kgavvala18/powergloveV2_LockheedMartin/reports/Individual reports/Brint Nielson/Individual Weekly Report 8.pdf

### Individual Weekly Report

Name: Brint Nielson
Team: The Gauntlet
Date: 3/29/2025

Current Status
1. What did you personally work on this past week?
Task | Status | Time Spent
Get driver example files and test drivers | In progress | 2 Hour
Adjust STL files for print casing and print casing | In progress | 3.5 hour

Include screenshots/graphics to illustrate what you did this past week:

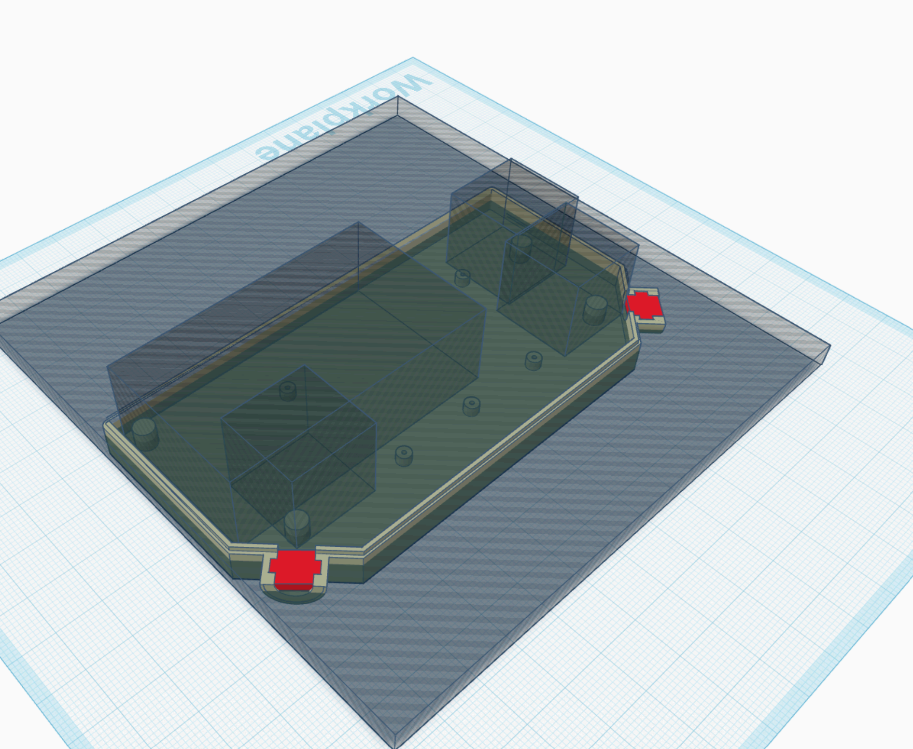
[picture p17: figure]

2. What problems did you run into? What is your plan for them? My 3d printer was giving me some issues but I was able to fix that.
3. What is the current overall project status from your perspective? Putting together for the final prototype/ testing.
4. How is your team functioning from your perspective?

Great we are close to finalizing and being able to test the integrated prototype.

5. What new ideas did you have or skills did you develop this week?
How to properly get my 3d printer to work and now learning how to test drivers.
6. Who was your most awesome team member this week and why?
I would put Will as the awesome team member of the week since he did great job starting the UI.

Plans for Next Week
What are you going to work on this next week?
Driver finalized and working with prototype and print and integrate final 3d prints.
