kgavvala18/powergloveV2_LockheedMartin/reports/Individual reports/Kris_Gavvala/weeklyUpdate3-24.pdf

### Individual Weekly Report

Name: Kris Gavvala
Team: PowerGlove
Date: 3/24/2025

Current Status
1. What did you personally work on this past week?
Task | Status | Time Spent
Implemented mouse clicks over usb hid | finished | 4 hours
Helped set connect all hardware for the prototype | finished | 2 hours

Include screenshots/graphics to illustrate what you did this past week:

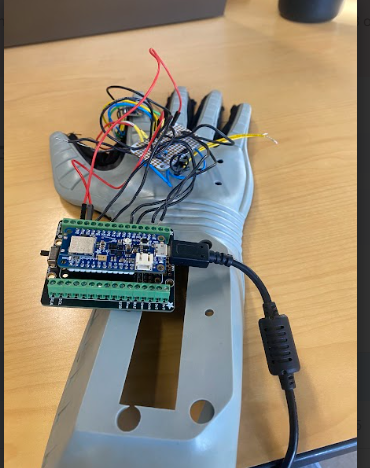
[picture p18: figure]

2. What problems did you run into? What is your plan for them?
Having some problems with keeping the cursor steady due to human movement imprecision. Need to create a dead zone when someone hovers over an object to click it.
3. What is the current overall project status from your perspective?
We are a little behind. We should finish the basic control movements this week and move into gesture control.
4. How is your team functioning from your perspective?
Pretty well. We are splitting up the work well.
5. What new ideas did you have or skills did you develop this week? Explored a little into using usb hid with a wireless transceiver.
6. Who was your most awesome team member this week and why?
Aaron was a great with putting together the prototype. He always shows up outside class to get work done and I really appreciate that.

Plans for Next Week
What are you going to work on this next week?

Going to figure out how to add functionality so that the mouse doesn’t move too much when trying to click.
