kgavvala18/powergloveV2_LockheedMartin/reports/Individual reports/Brint Nielson/Individual Weekly Report 7.pdf

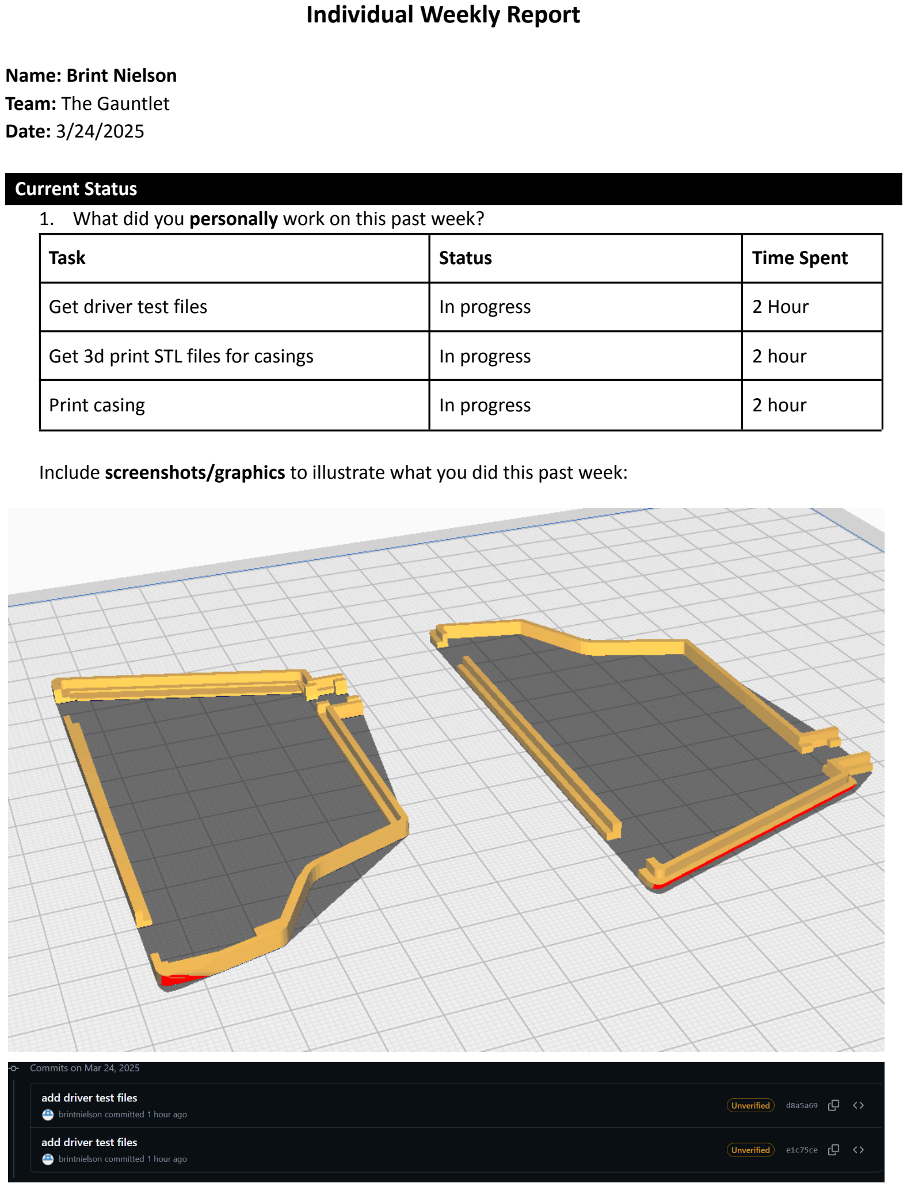
[picture p19: page 1]

### Individual Weekly Report

Name: Brint Nielson
Team: The Gauntlet
Date: 3/24/2025

Current Status
1. What did you personally work on this past week?
Task | Status | Time Spent
Get driver test files | In progress | 2 Hour
Get 3d print STL files for casings | In progress | 2 hour
Print casing | In progress | 2 hour

Include screenshots/graphics to illustrate what you did this past week:

2. What problems did you run into? What is your plan for them?
Was sick the last week but the next week I should be much more free so I will be working on it overtime.
3. What is the current overall project status from your perspective?
The prototype stage and next stage is to make it look good and work even better.
4. How is your team functioning from your perspective?
Great we have been making great progress so far.
5. What new ideas did you have or skills did you develop this week?
I was able to get more 3d print designs and learning more how that works.
6. Who was your most awesome team member this week and why?
I would put Grant for putting together the really small soldering of the encoders.

Plans for Next Week
What are you going to work on this next week?
Finalize driver testing and get a good print going for our casings.
