kgavvala18/powergloveV2_LockheedMartin/reports/Individual reports/Kris_Gavvala/Individual_report_3-17.pdf

### Individual Weekly Report

Name: Kris Gavvala
Team: PowerGlove
Date: 3/17/2025

Current Status
1. What did you personally work on this past week?
Task | Status | Time Spent
Implemented an extended Kalman filter to Process data from IMU | finished | 4 days
Designed the circuit for the laser pointer | finished | 2 hours
Did some planning for gesture features | finished | 2 hours

Include screenshots/graphics to illustrate what you did this past week:

Gyroscope Filtered Data vs measurements:

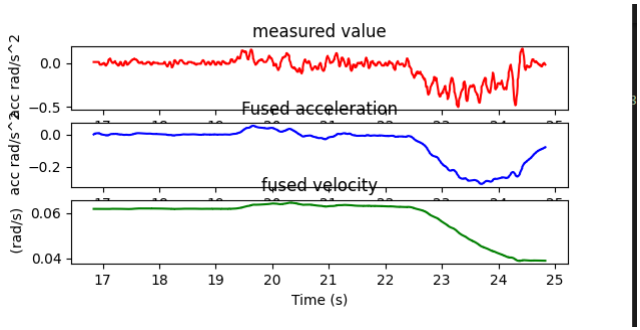
[picture p20: figure]

Arduino C code of Kalman Filter Implementation

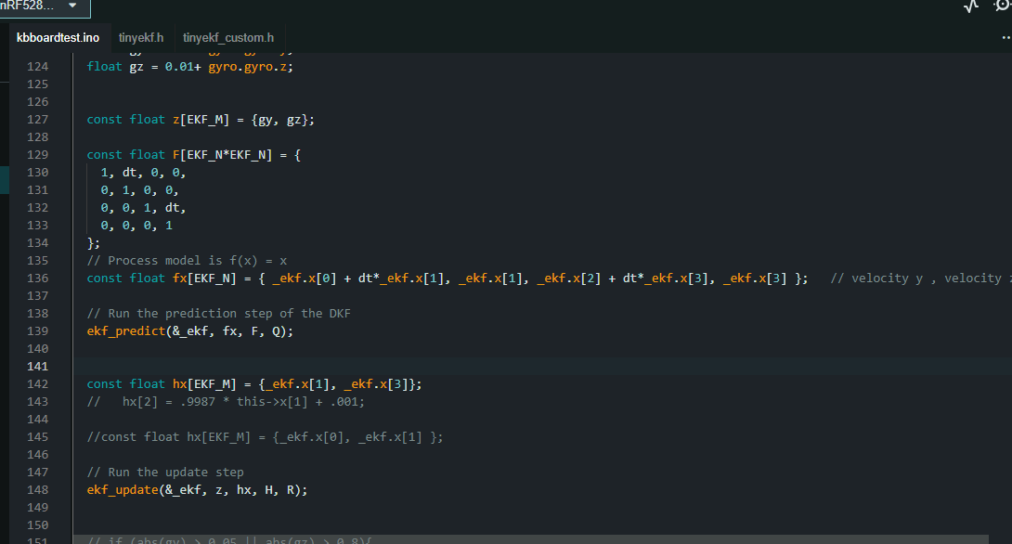
[picture p21: figure]

2. What problems did you run into? What is your plan for them?
We were having trouble with jitter when translating our sensor data into mouse control. To solve this I implemented a kalman filter to smooth the data in real-time for better mouse control.
One problem I still need to solve is getting the glove to keep track of its location in space so it can stay locked onto the mouse without much calibration. I will explore different strategies with the magnetometer to track its initial starting point and motion so that it stays with the mouse.
3. What is the current overall project status from your perspective?
We are slightly behind. We plan to get all current hardware into the glove by the end of this week and start testing the full product.
4. How is your team functioning from your perspective?
We are doing good. We all have defined roles for this week and should be in position to finish up base requirements and move into some stretch goals.
5. What new ideas did you have or skills did you develop this week?
I learned a lot about kalman filters and extended kalman filters. I got some more experience using matlab to test math before putting it into code.

6. Who was your most awesome team member this week and why?
Grant was good this week. He did some good work with coding the buttons.

Plans for Next Week
What are you going to work on this next week?
- Moving parts into the glove
- Tuning the cursor movement so that it accurately stays with the mouse even when the glove’s angular acceleration takes it off-screen.
- Design 3d printed housing to put both accelerometer and laser on the finger.
- Tune mouse movement so that it accounts for both accelerometer movement and gyroscope movement.
