kgavvala18/powergloveV2_LockheedMartin/reports/Individual reports/Brint Nielson/Individual Weekly Report 5.pdf

### Individual Weekly Report

Name: Brint Nielson
Team: The Gauntlet
Date: 3/3/2025

Current Status
1. What did you personally work on this past week?
Task | Status | Time Spent
Get left ctrl modifiers to work to allow more versatility in inputs from the glove | Complete | 1.5 hours
Work on getting integrate mouse movement to be more smooth | In progress | 2 hours
Start driver development | In progress | 50 mins

Include screenshots/graphics to illustrate what you did this past week:

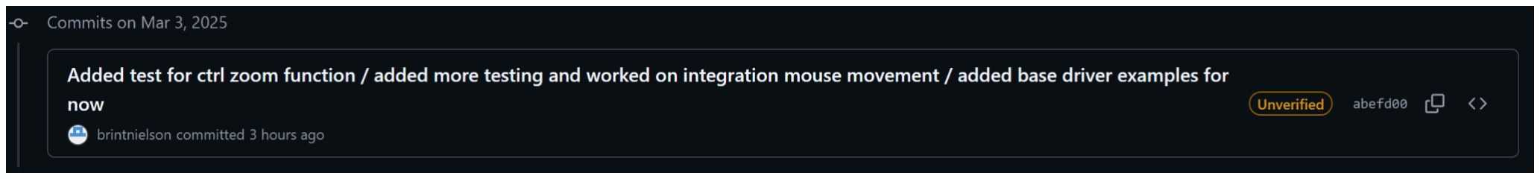
[picture p24: figure]

2. What problems did you run into? What is your plan for them?
So far just slower than expected progress for mouse integration but planning to work on it more this week since I should have more time this week after my test then last week.
3. What is the current overall project status from your perspective?
Finished most testing of hardware and now integrating the hardware and refining the software to make it work better.
4. How is your team functioning from your perspective?
Great we have been making good progress so far.
5. What new ideas did you have or skills did you develop this week?
Learned how drivers work and how to further make our mouse controls work the way we want them too.
6. Who was your most awesome team member this week and why?

I would put Aaron since he sent us a video update for how the glove had the flex sensors in it and worked with it.

Plans for Next Week
What are you going to work on this next week?
I want to get mouse movement working much better and finish learning about drivers and hopefully finish those up.
