kgavvala18/powergloveV2_LockheedMartin/reports/Individual reports/Aaron/IndividualReport8.pdf

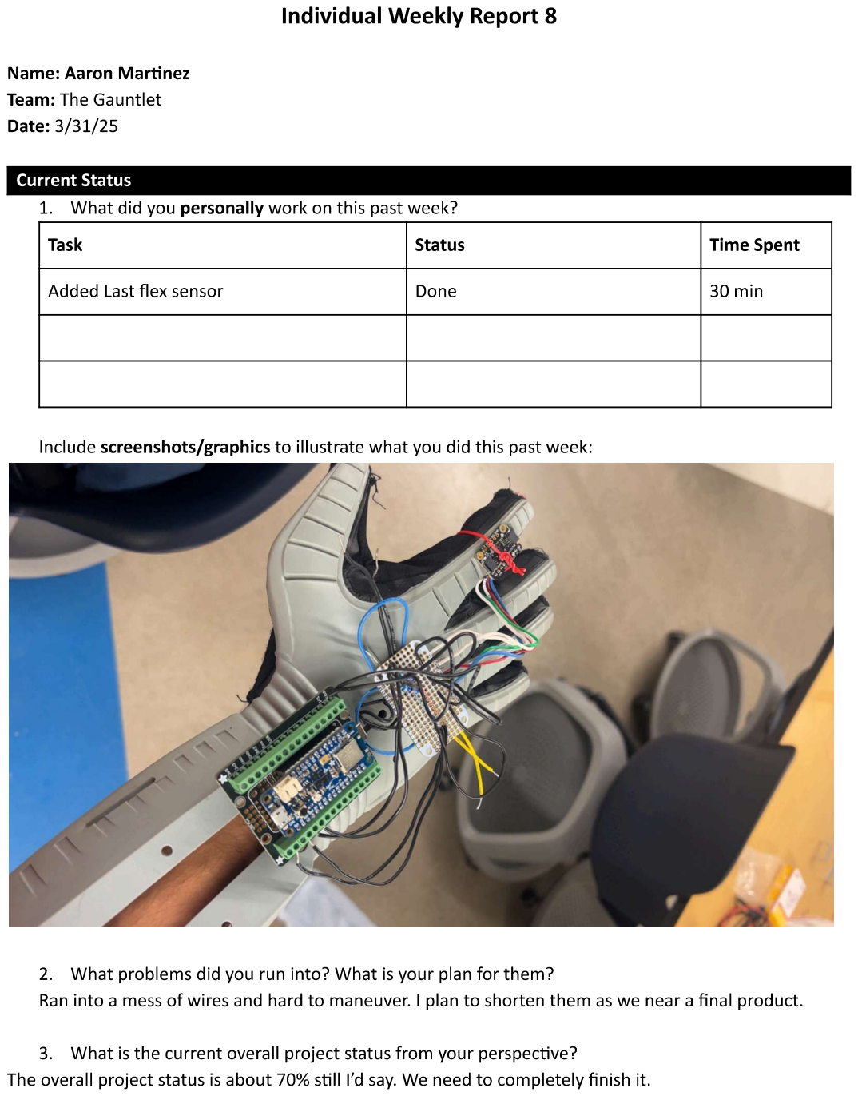
[picture p41: page 1]

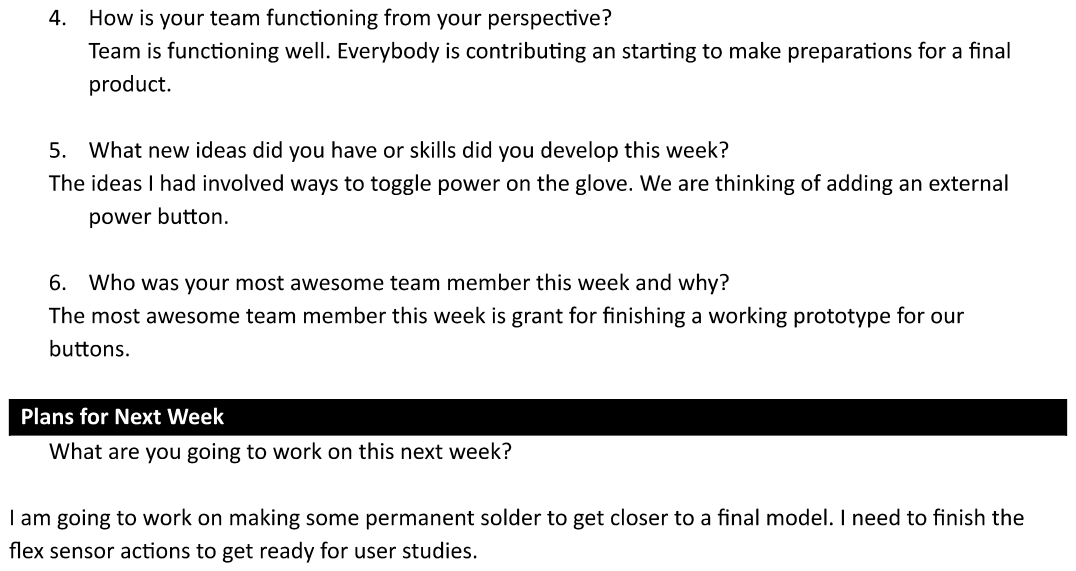
[picture p42: page 2]
