kgavvala18/powergloveV2_LockheedMartin/reports/Individual reports/Aaron/IndividualReport7.pdf

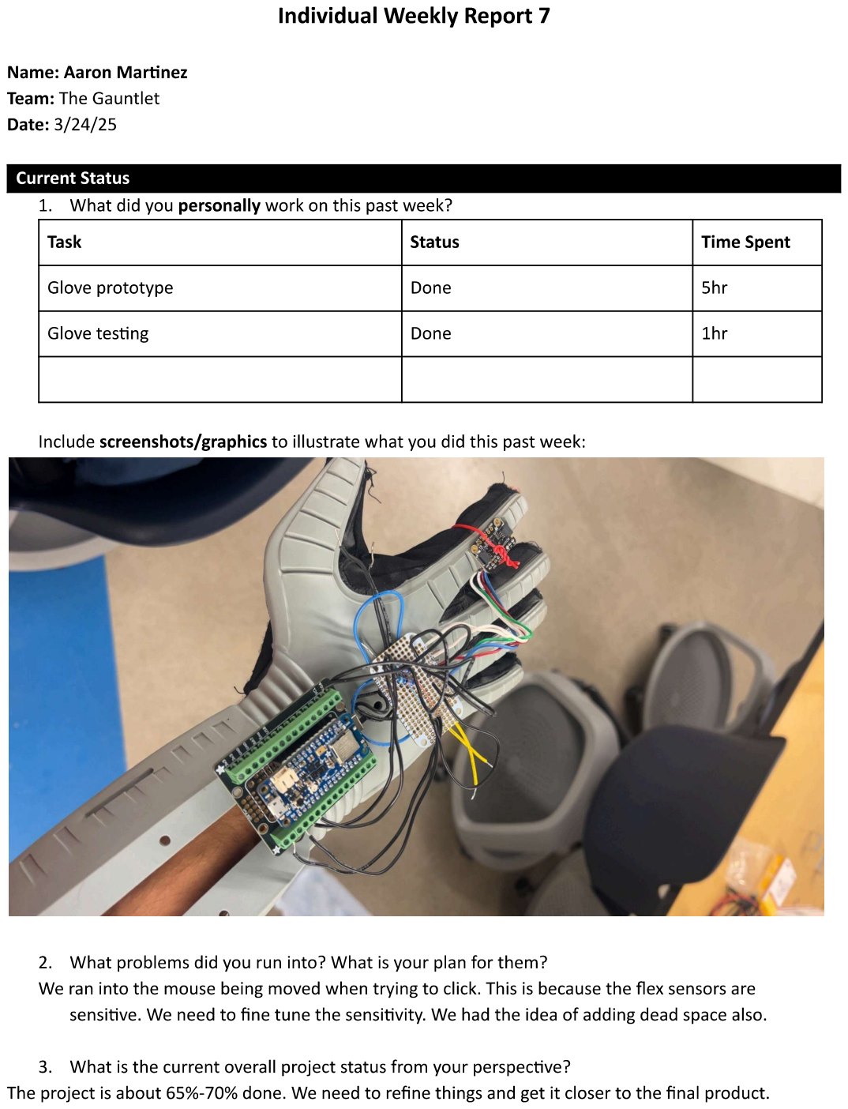
[picture p43: page 1]

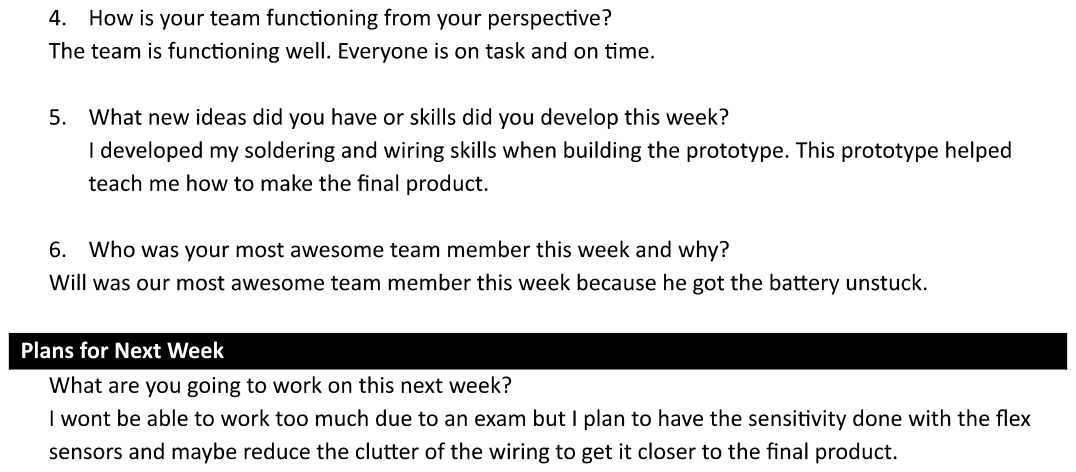
[picture p44: page 2]
