kgavvala18/powergloveV2_LockheedMartin/reports/Individual reports/Aaron/IndividualReport6.pdf

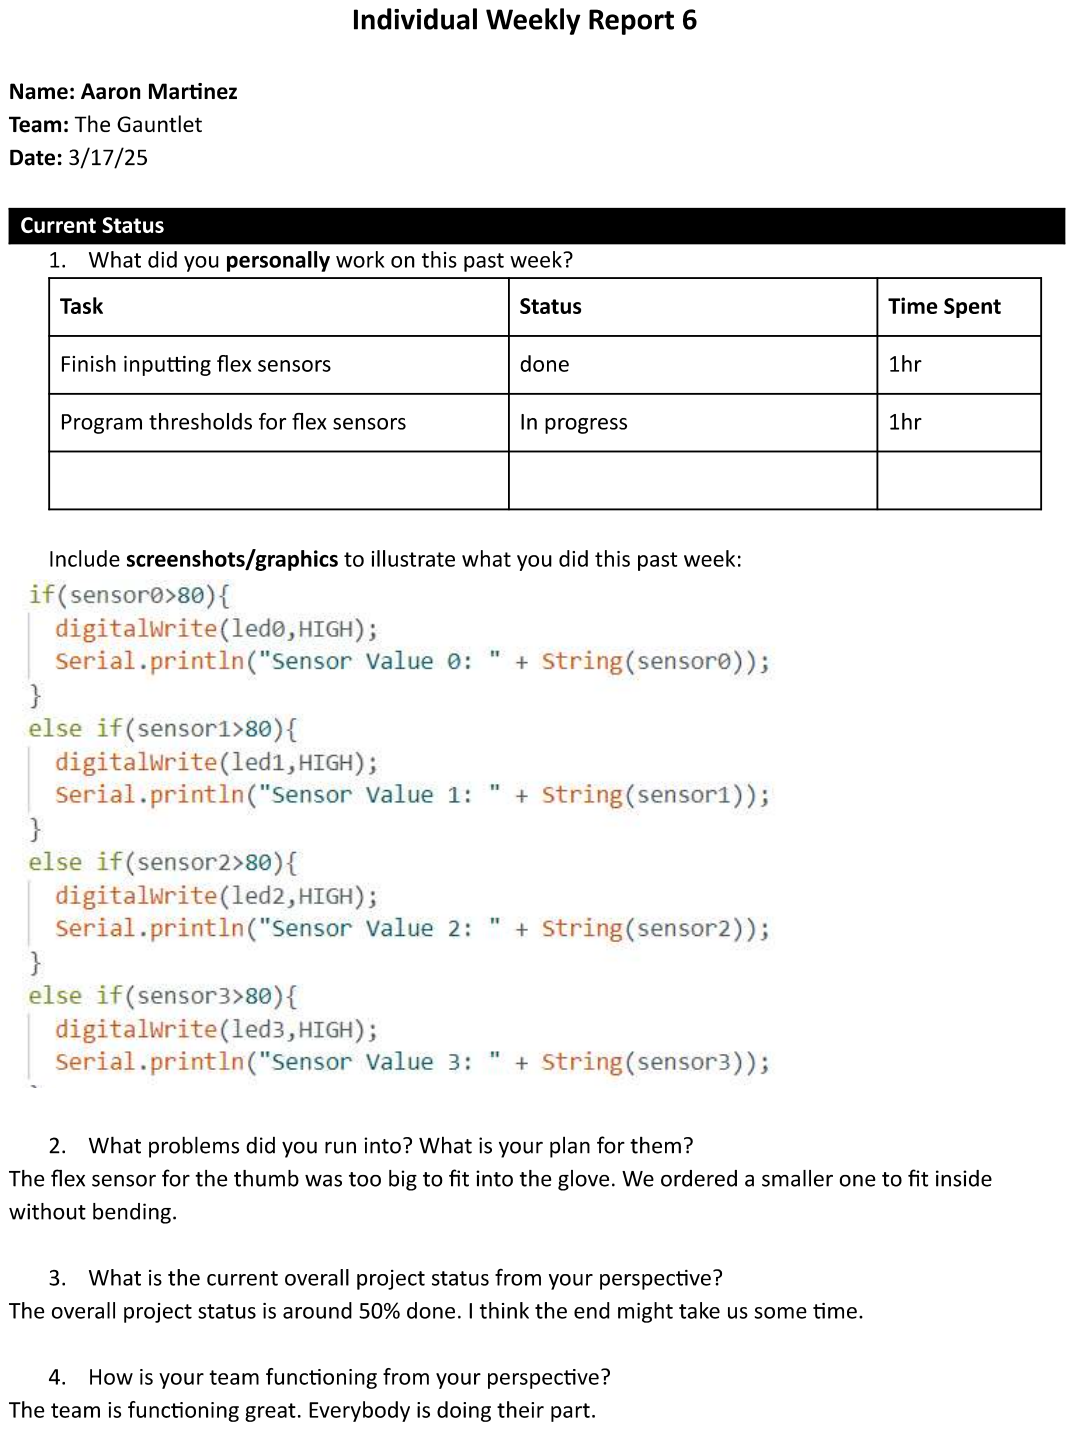
[picture p45: page 1]

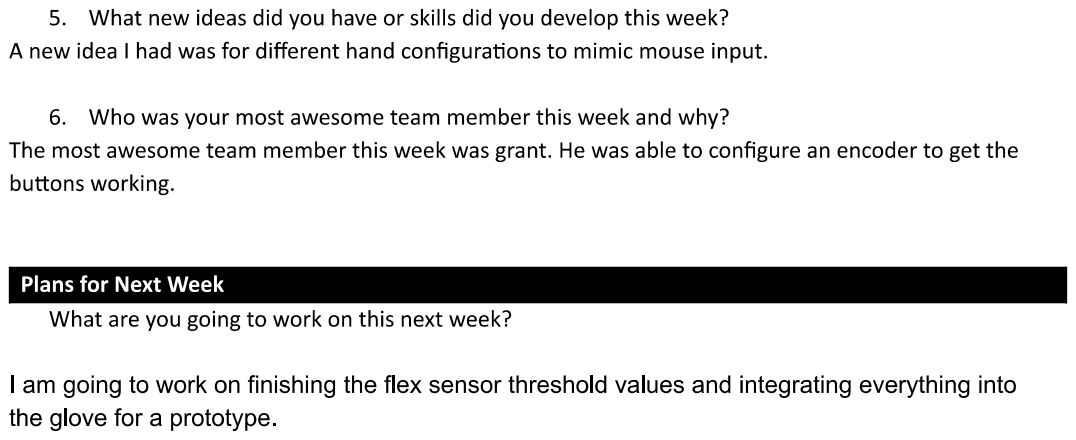
[picture p46: page 2]
