kgavvala18/powergloveV2_LockheedMartin/reports/Individual reports/Aaron/IndividualReport5.pdf

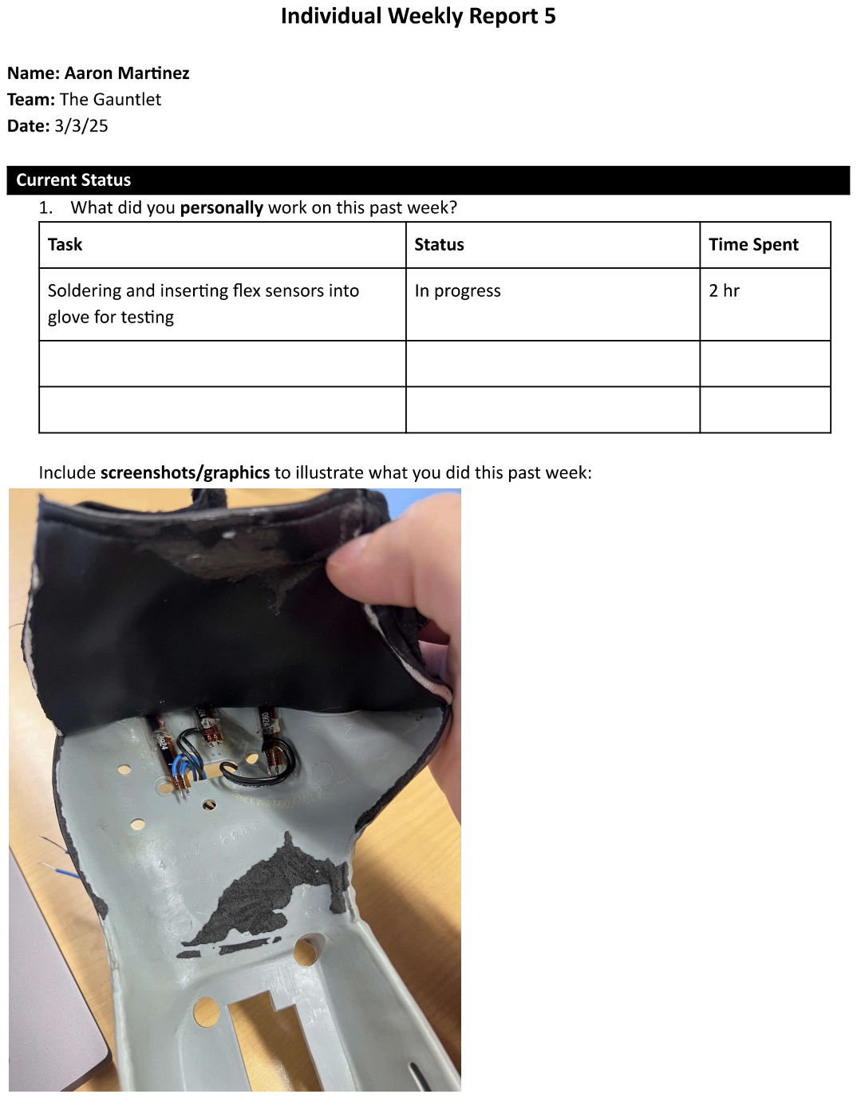
[picture p47: page 1]

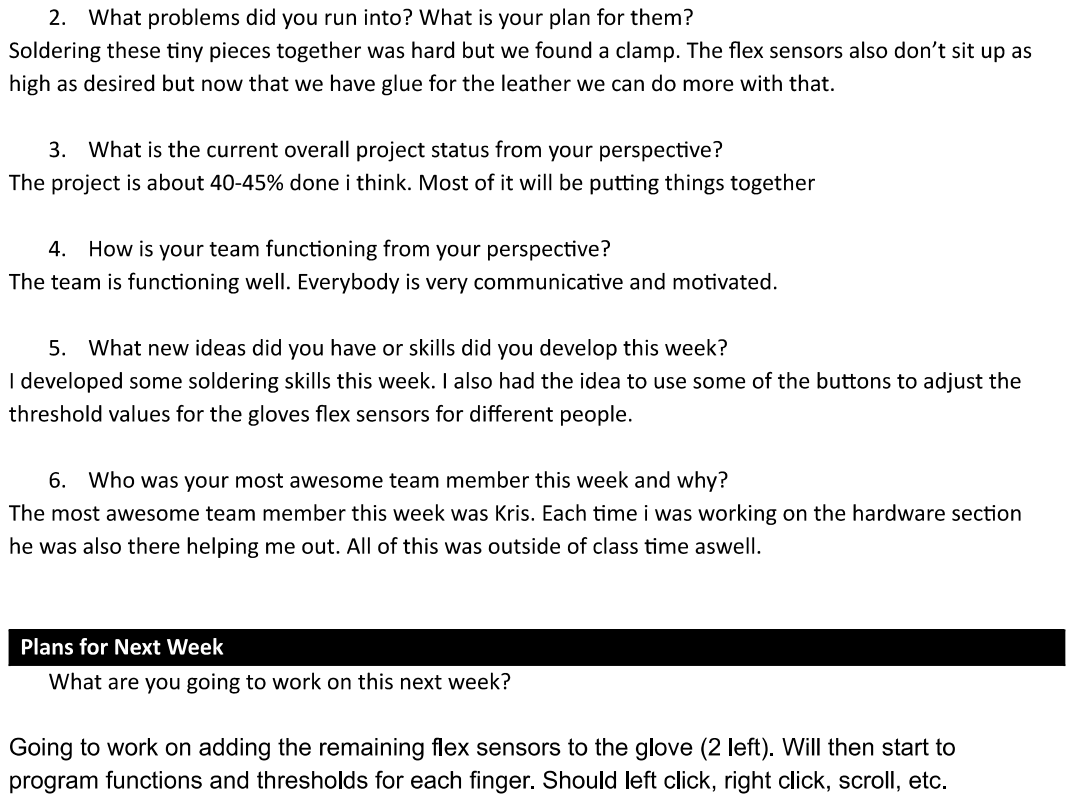
[picture p48: page 2]
